Radacon/MouseMinder/mechanical_design/trap_body/005_Boss-Extrude11[13].step

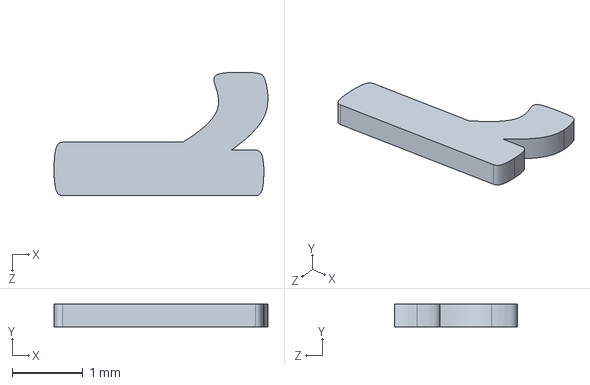
[picture p15: CAD file, 2026-04-10]
mechanical_design/trap_body/005_Boss-Extrude11[13].step
3.03 x 0.32 x 1.75 mm
