Radacon/MouseMinder/mechanical_design/trap_body/008_Lid.step

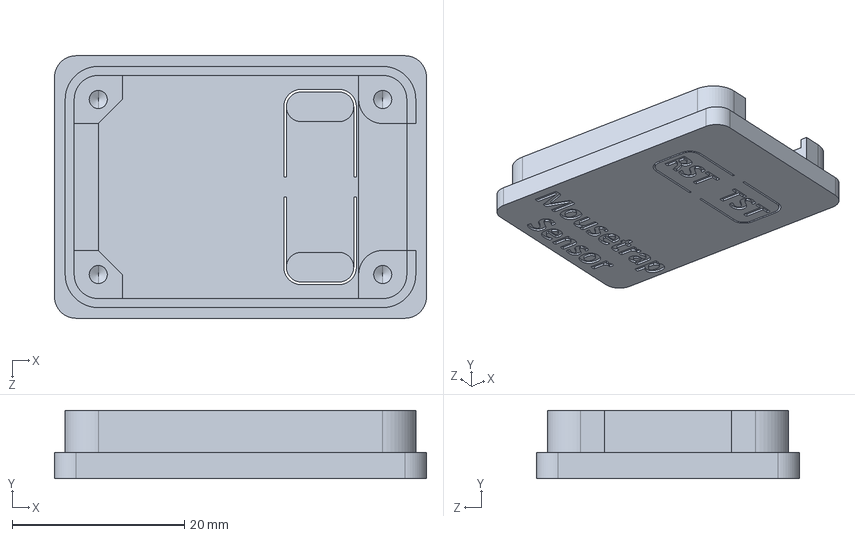
[picture p16: CAD file, 2026-04-10]
mechanical_design/trap_body/008_Lid.step
43.2 x 7.93 x 30.5 mm
