Radacon/MouseMinder/mechanical_design/trap_body/013_Boss-Extrude11[11].step

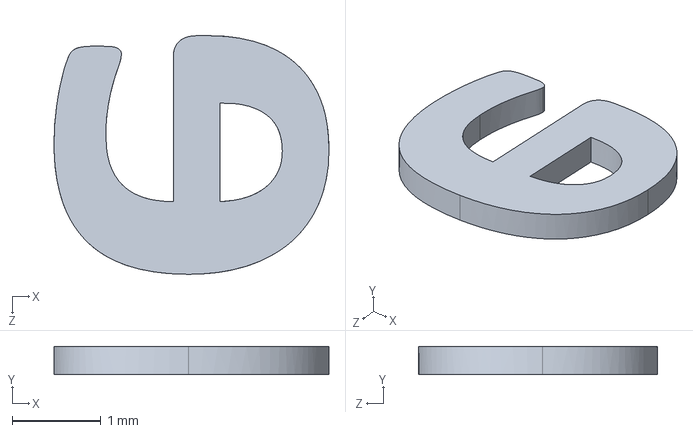
[picture p17: CAD file, 2026-04-10]
mechanical_design/trap_body/013_Boss-Extrude11[11].step
3.09 x 0.32 x 2.68 mm
